MOSH-Insa-Toulouse/cres-limouzy-malique-gazsensor/images/node-red-interface.PNG

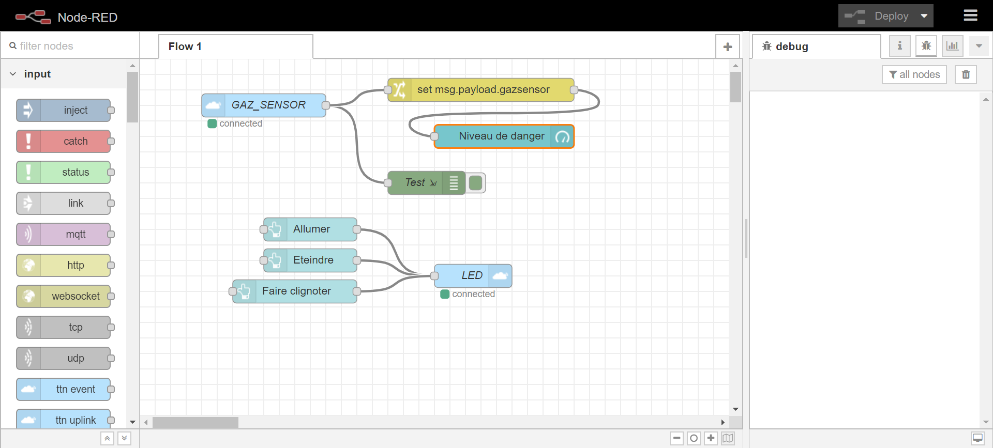
images/node-red-interface.PNG
