MOSH-Insa-Toulouse/cres-limouzy-malique-gazsensor/images/node-red-ui.PNG

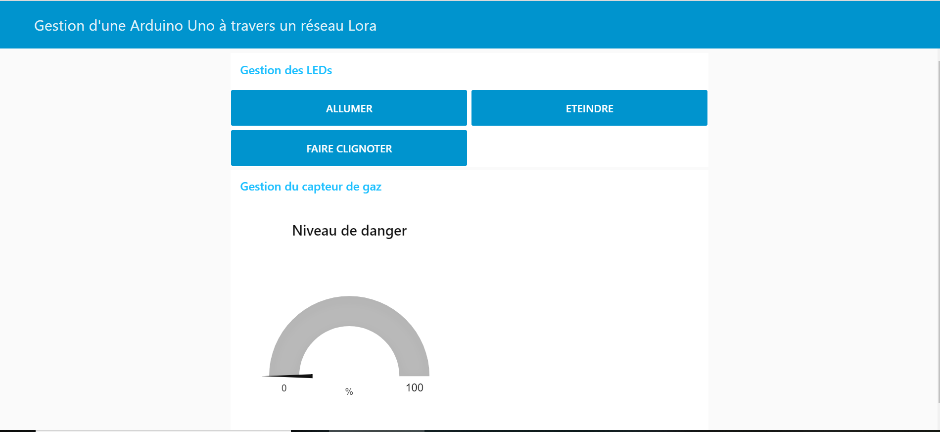
images/node-red-ui.PNG
